SteveLRojas/usb_button_interface/SW/ubi_regs.py

R_DEVICE_ID_LL = 0X00
R_DEVICE_ID_LH = 0X01
R_DEVICE_ID_HL = 0X02
R_DEVICE_ID_HH = 0X03

R_UNIQUE_ID_LL = 0X04
R_UNIQUE_ID_LH = 0X05
R_UNIQUE_ID_HL = 0X06
R_UNIQUE_ID_HH = 0X07

R_MAP_IDX = 0x08
R_MAP_DATA = 0x09
R_LOAD_KEY_MAP = 0x0A
R_WRITE_KEY_MAP = 0x0B
R_BLANK_MAP_ADDR = 0x0C
R_EEPROM_IDX = 0x0D
R_EEPROM_DATA = 0x0E
R_EEPROM_CLEAR = 0x0F
